Bizunow/monoflex-keyboard/case_design/monoflex_bottom.step

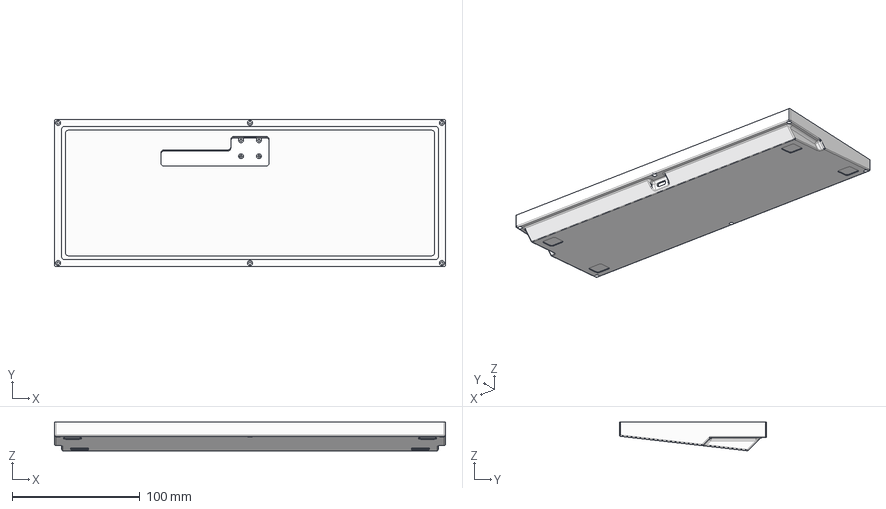
[picture p15: CAD file, 2021-12-04]
case_design/monoflex_bottom.step
305.8 x 115.2 x 22.4 mm
